oresat/system-controller/firmware/adc.c

#include "adc.h"

bool adc_init(){
    /*
     voltage reference selection
     AVCC w/ external cap at AREF pin
     */
    return (setBit(&ADMUX, REFS0) &&
            clearBit(&ADMUX, REFS1) &&
            clearBit(&ADMUX, ADLAR) &&
            clearBit(&ADMUX, MUX4) &&
            clearBit(&ADMUX, MUX3) &&
            clearBit(&ADMUX, MUX2) &&
            clearBit(&ADMUX, MUX1) &&
            clearBit(&ADMUX, MUX0) &&
            /*
             set prescalar to 2
             this divides F_CPU by 2
             for ADC clock frequency
             */
            clearBit(&ADCSRA, ADPS2) &&
            clearBit(&ADCSRA, ADPS1) &&
            clearBit(&ADCSRA, ADPS0) &&
           	/*
             enable ADC in free run mode
             */
            setBit(&ADCSRA, ADEN) &&
            setBit(&ADCSRA, ADFR));
}

uint16_t adc_read(){
    /* grab last two bits from ADCH register */
    uint8_t ADCHigh = ADCH & 0x3;
    
    /* grab contents of ADCL register */
    uint8_t ADCLow = ADCL;
    
    return ((ADCHigh << 8) | ADCLow);
}
